mikelawrence/esphome-indoor-multi-sensor/enclosure/3d-printing/ESPHome-Multi-Sensor-Enclosure-Back-Mount-15°.step

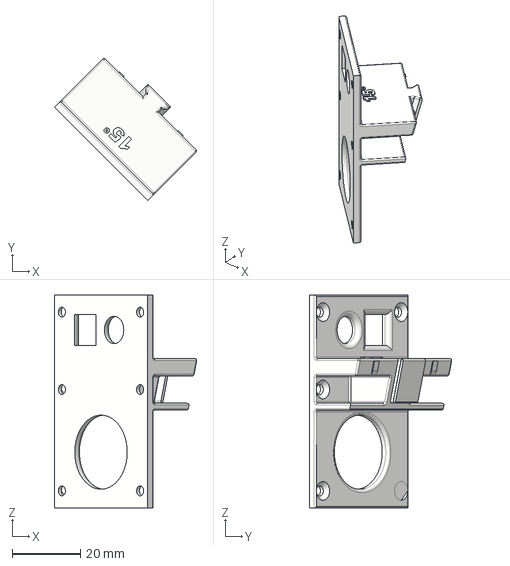
[picture p20: CAD file, 2025-04-12]
enclosure/3d-printing/ESPHome-Multi-Sensor-Enclosure-Back-Mount-15°.step
41.6 x 41.6 x 62.2 mm
