mikelawrence/esphome-indoor-multi-sensor/pcb/3dmodels/RSM-105-02-S-S.stp

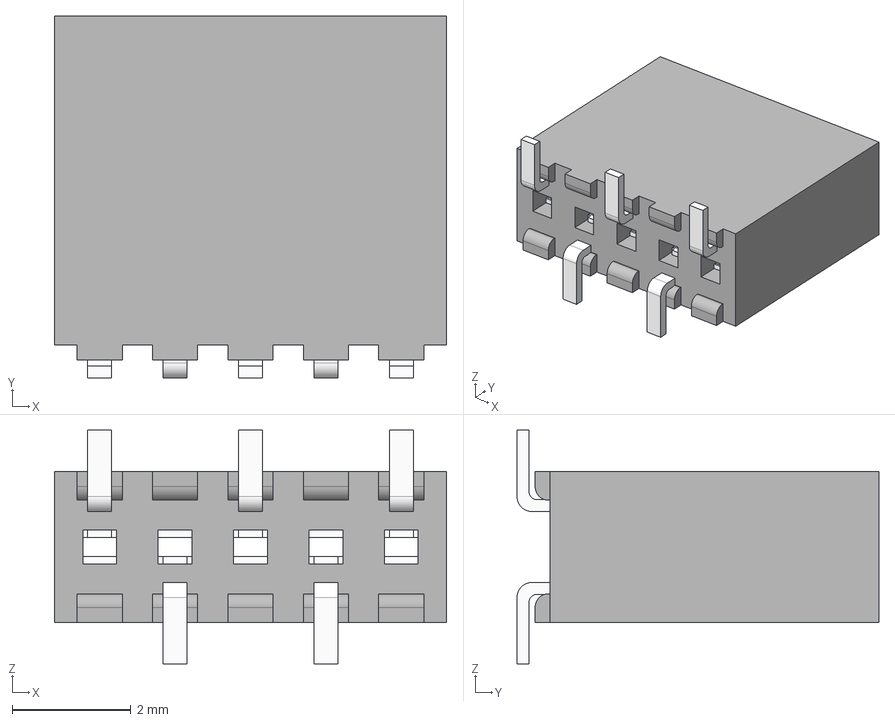
[picture p21: CAD file, 2025-04-11]
pcb/3dmodels/RSM-105-02-S-S.stp
6.60 x 6.10 x 3.94 mm
RSM-105-02-S_socket
C-64-02-05-SS
C-64-02-05-SS2
