mikelawrence/esphome-indoor-multi-sensor/enclosure/3d-printing/ESPHome-Multi-Sensor-Enclosure-Corner-Mount-5°.step

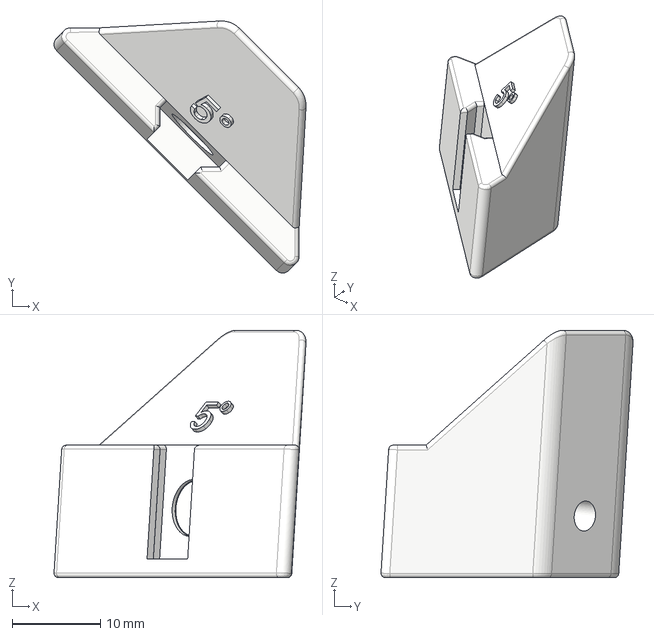
[picture p22: CAD file, 2025-04-12]
enclosure/3d-printing/ESPHome-Multi-Sensor-Enclosure-Corner-Mount-5°.step
28.5 x 28.5 x 28.0 mm
