mikelawrence/esphome-indoor-multi-sensor/pcb/3dmodels/SHT45-AD1B-R2--3DModel-STEP-369182.STEP

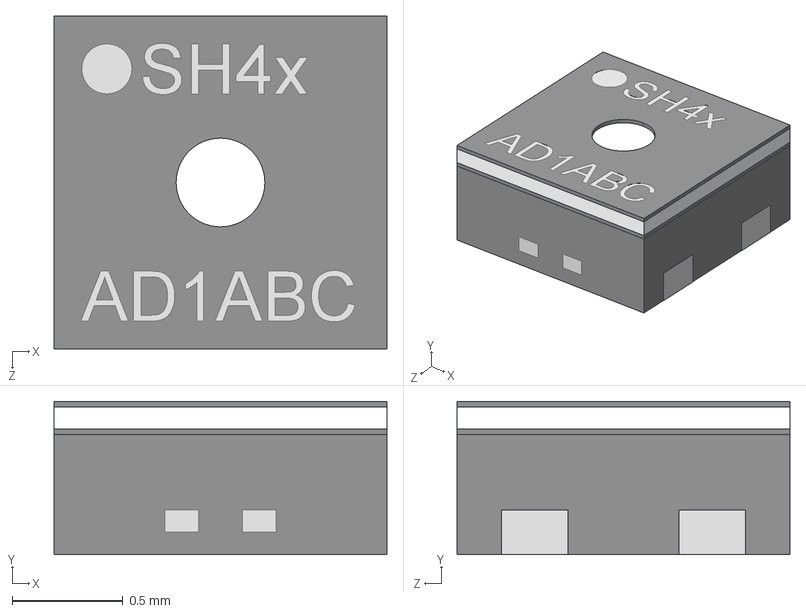
[picture p23: CAD file, 2025-04-11]
pcb/3dmodels/SHT45-AD1B-R2--3DModel-STEP-369182.STEP
1.50 x 0.691 x 1.50 mm
