mikelawrence/esphome-indoor-multi-sensor/enclosure/3d-printing/ESPHome-Multi-Sensor-Enclosure-Speaker-25mmx14mm.step

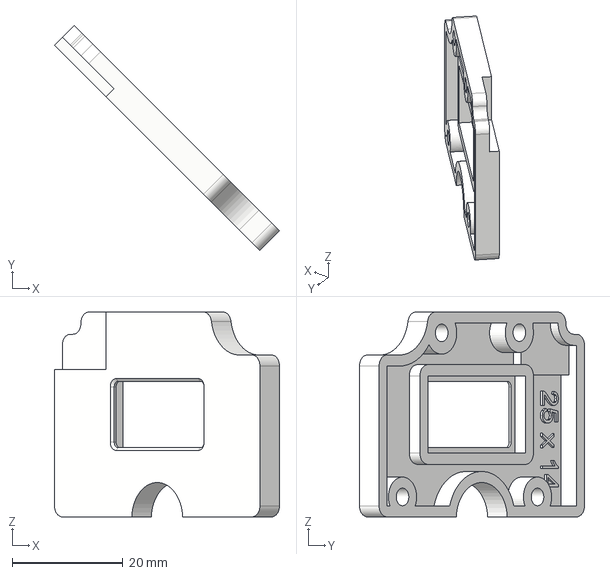
[picture p24: CAD file, 2025-04-12]
enclosure/3d-printing/ESPHome-Multi-Sensor-Enclosure-Speaker-25mmx14mm.step
40.7 x 40.7 x 37.0 mm
