mikelawrence/esphome-indoor-multi-sensor/enclosure/3d-printing/ESPHome-Multi-Sensor-Enclosure Front Body.step

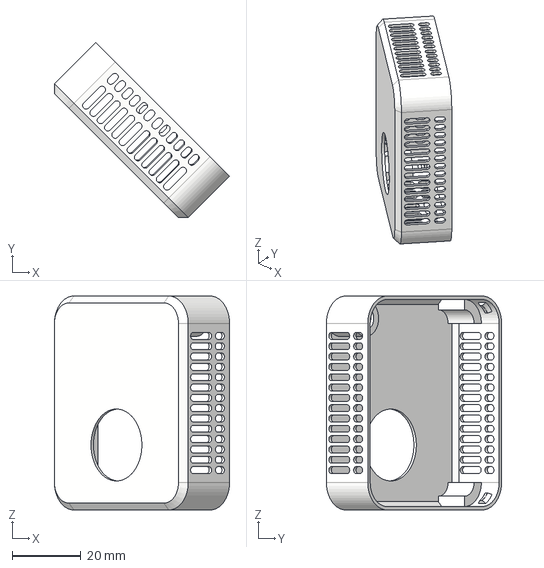
[picture p26: CAD file, 2025-04-12]
enclosure/3d-printing/ESPHome-Multi-Sensor-Enclosure Front Body.step
50.9 x 50.9 x 62.2 mm
