mikelawrence/esphome-indoor-multi-sensor/pcb/3dmodels/ast-ind-250605.STEP

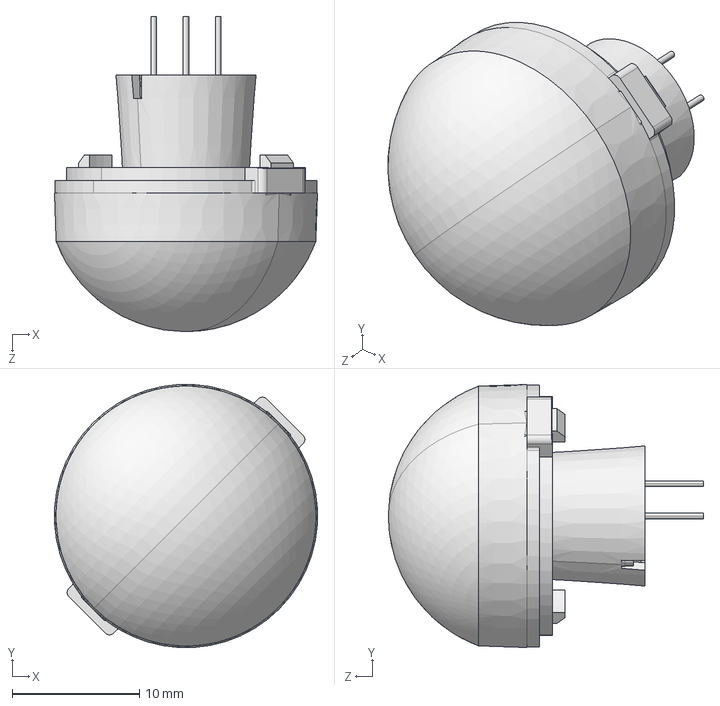
[picture p27: CAD file, 2025-04-11]
pcb/3dmodels/ast-ind-250605.STEP
20.7 x 20.7 x 24.8 mm
