mikelawrence/esphome-indoor-multi-sensor/enclosure/3d-printing/ESPHome-Multi-Sensor-Enclosure-Corner-Mount-25°.step

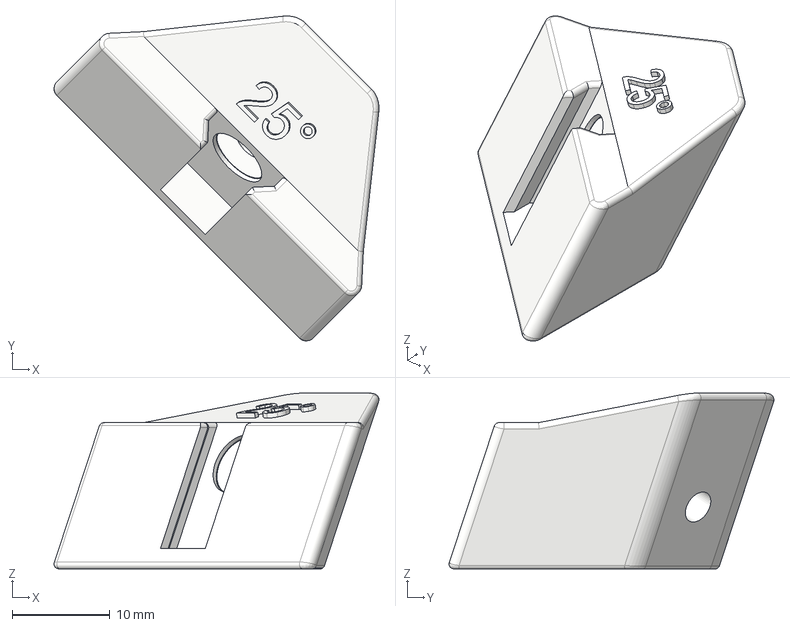
[picture p28: CAD file, 2025-04-12]
enclosure/3d-printing/ESPHome-Multi-Sensor-Enclosure-Corner-Mount-25°.step
33.3 x 33.3 x 18.0 mm
