mikelawrence/esphome-indoor-multi-sensor/pcb/3dmodels/WS2812-2020--3DModel-STEP-1.STEP

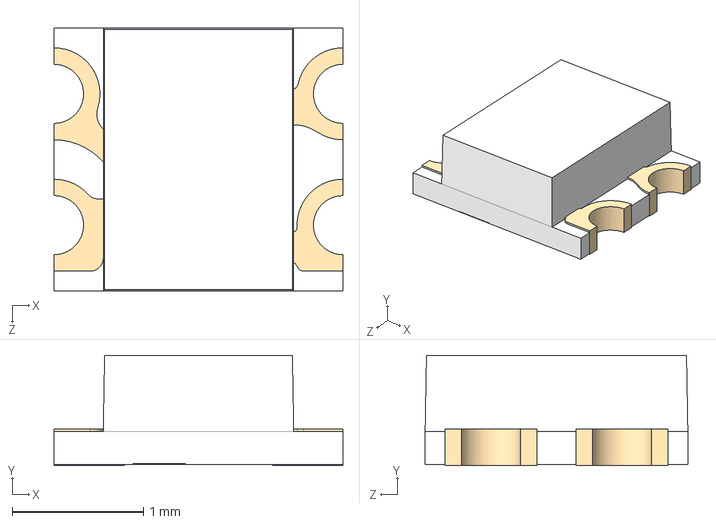
[picture p29: CAD file, 2025-04-11]
pcb/3dmodels/WS2812-2020--3DModel-STEP-1.STEP
2.20 x 0.84 x 2.00 mm
