mikelawrence/esphome-indoor-multi-sensor/enclosure/3d-printing/ESPHome-Multi-Sensor-Enclosure-Back-Mount-20°.step

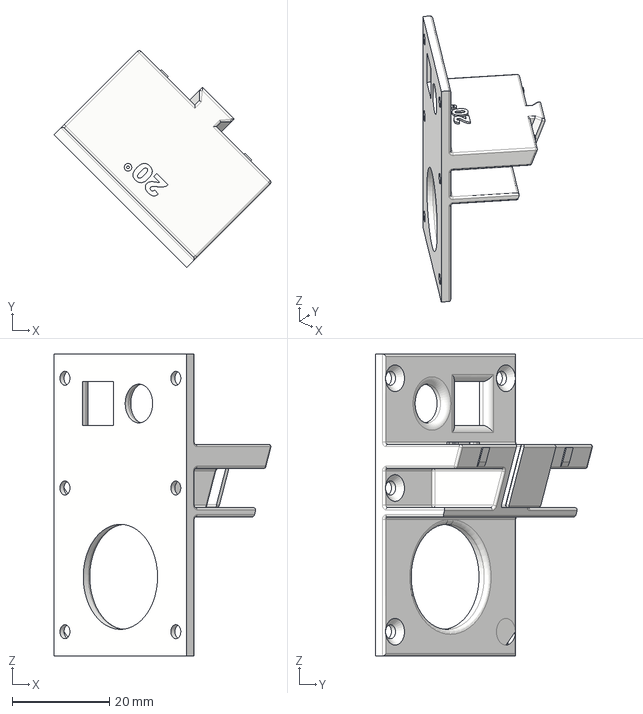
[picture p30: CAD file, 2025-04-12]
enclosure/3d-printing/ESPHome-Multi-Sensor-Enclosure-Back-Mount-20°.step
44.6 x 44.6 x 62.2 mm
