mikelawrence/esphome-indoor-multi-sensor/pcb/3dmodels/ESP32-S3-MINI-1-N8--3DModel-STEP-1.STEP

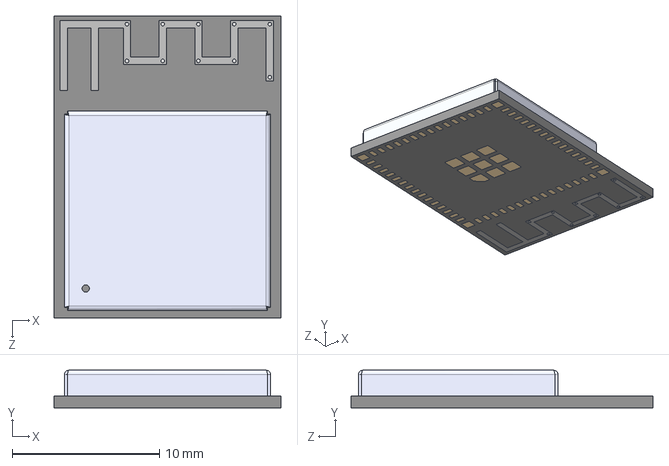
[picture p31: CAD file, 2025-04-11]
pcb/3dmodels/ESP32-S3-MINI-1-N8--3DModel-STEP-1.STEP
15.4 x 2.55 x 20.5 mm
