mikelawrence/esphome-indoor-multi-sensor/pcb/3dmodels/TLW-105-06-T-S.stp

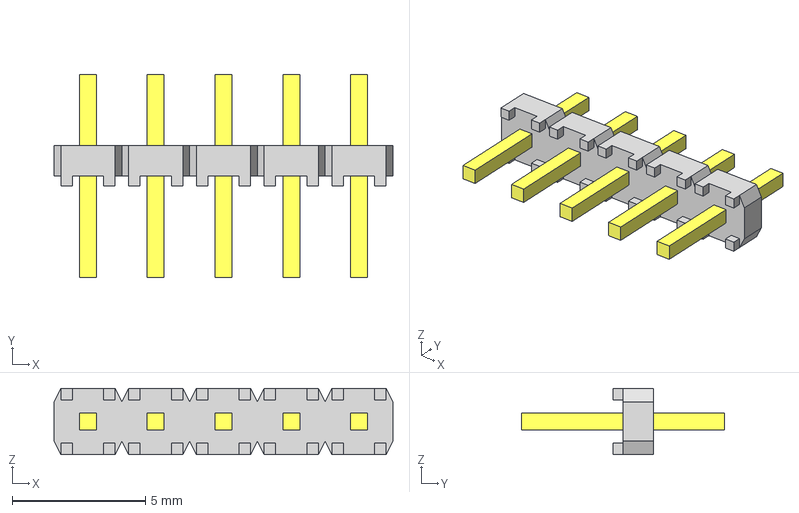
[picture p33: CAD file, 2025-04-11]
pcb/3dmodels/TLW-105-06-T-S.stp
12.7 x 7.62 x 2.49 mm
TLW-105-06-T-S_terminal
TLW-05-06-S0.3
