mikelawrence/esphome-indoor-multi-sensor/pcb/3dmodels/HLK-2410B.step

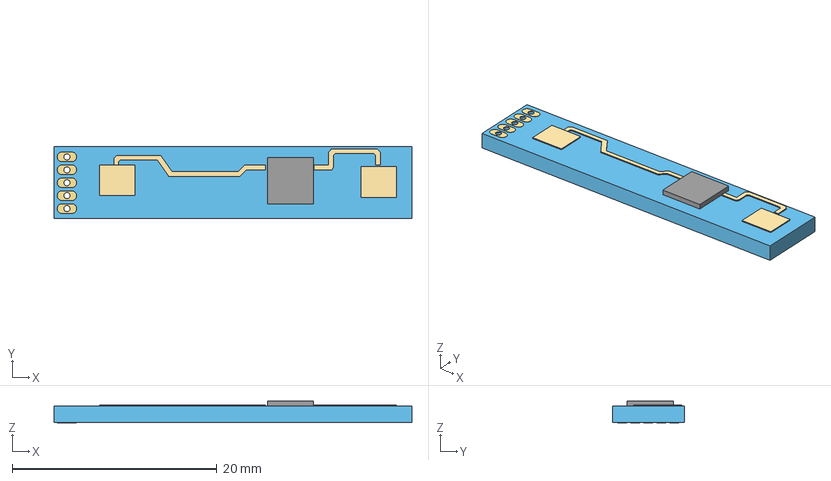
[picture p34: CAD file, 2025-04-11]
pcb/3dmodels/HLK-2410B.step
35.0 x 7.00 x 2.15 mm
